rayozzie/redbee/Photos/20160505_203314.jpg

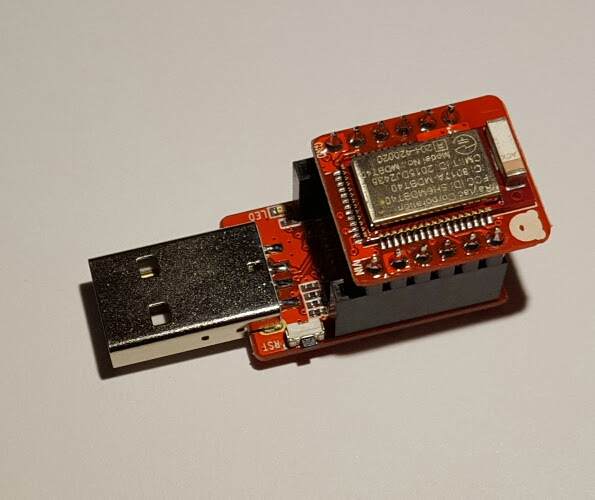
Photos/20160505_203314.jpg
