rayozzie/redbee/Photos/20160505_203927.jpg

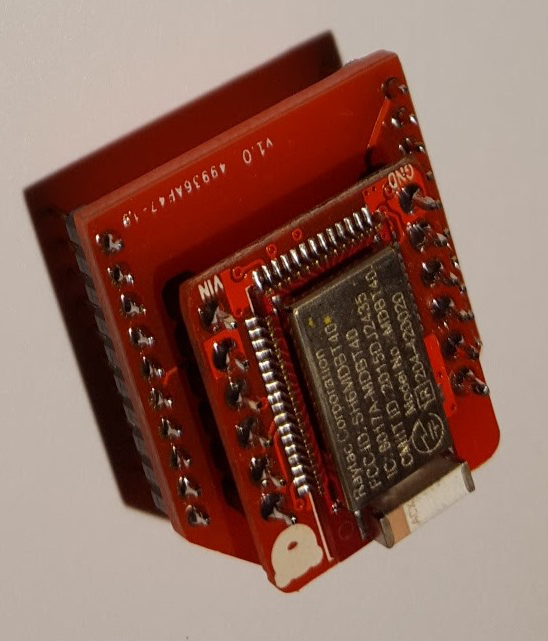
Photos/20160505_203927.jpg
