rayozzie/redbee/Photos/20160505_203952.jpg

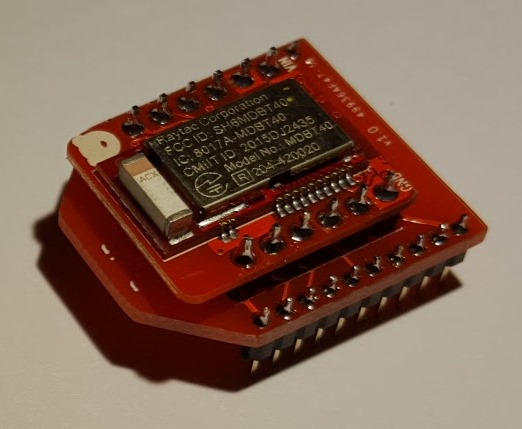
Photos/20160505_203952.jpg
