rayozzie/redbee/Photos/20160505_204019.jpg

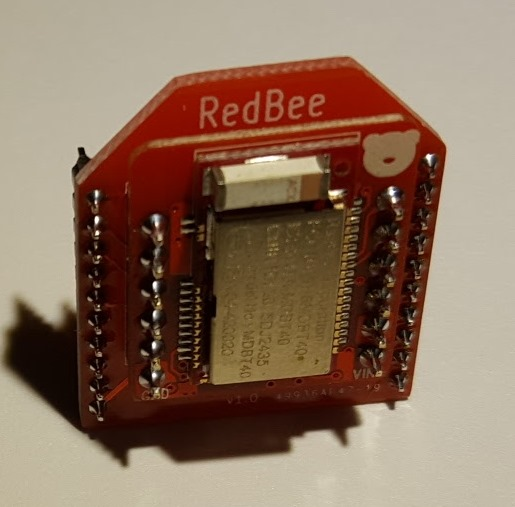
Photos/20160505_204019.jpg
