rayozzie/redbee/Photos/20160505_204045.jpg

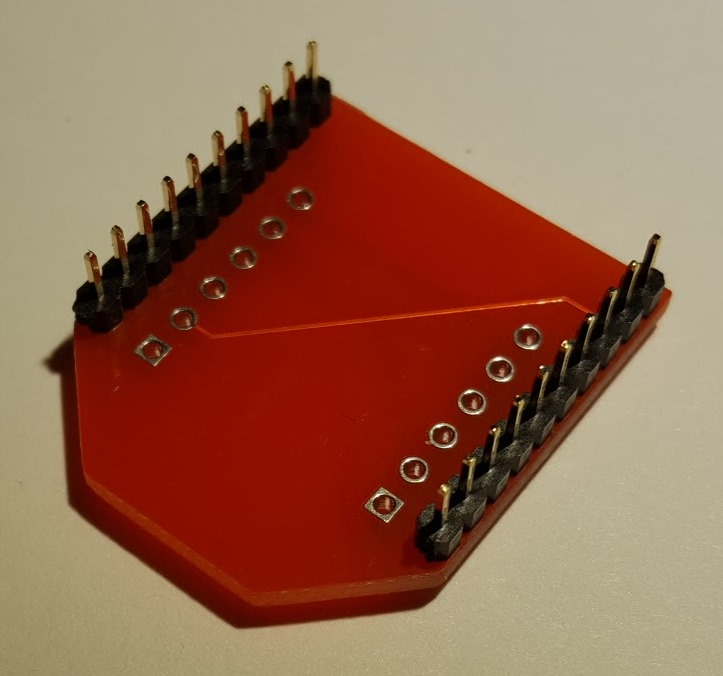
Photos/20160505_204045.jpg
