rayozzie/redbee/Photos/20160505_204118.jpg

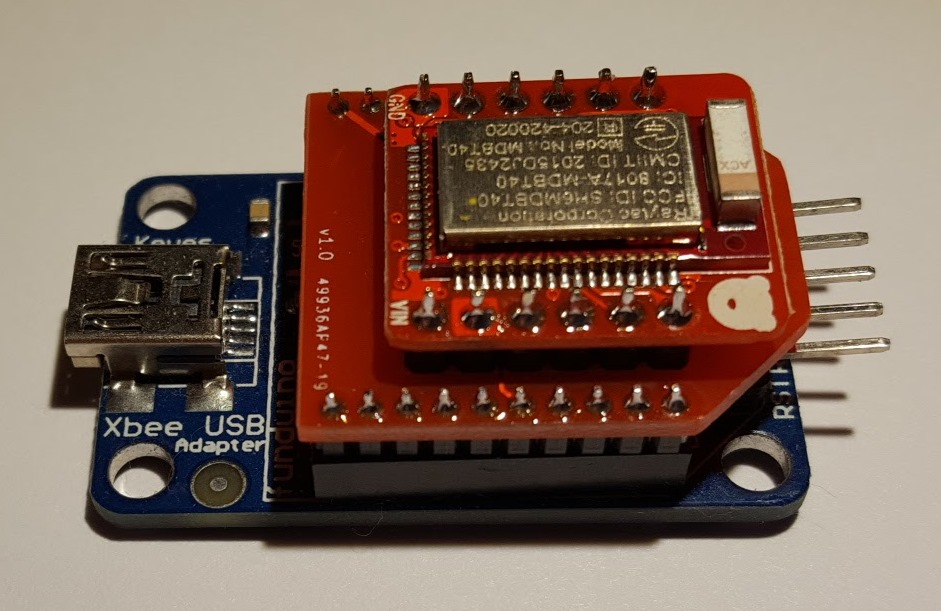
Photos/20160505_204118.jpg
