rayozzie/redbee/Photos/20160505_204125.jpg

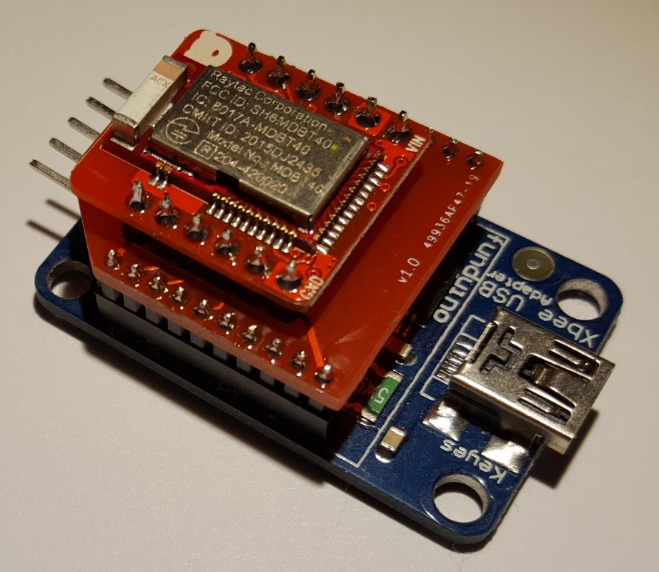
Photos/20160505_204125.jpg
