rayozzie/redbee/Photos/20160505_204313.jpg

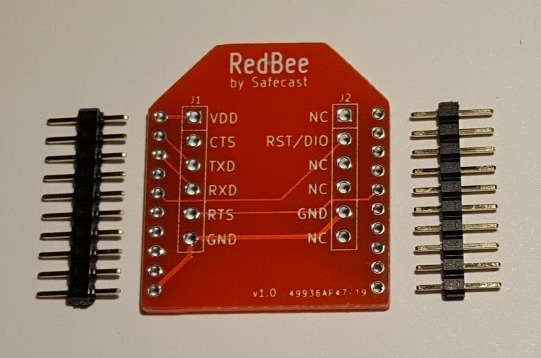
Photos/20160505_204313.jpg
