rayozzie/redbee/Photos/20160505_204332.jpg

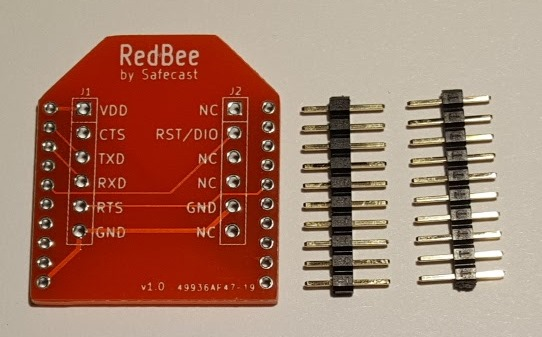
Photos/20160505_204332.jpg
