rayozzie/redbee/Photos/20160505_204348.jpg

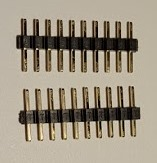
Photos/20160505_204348.jpg
