rayozzie/redbee/Photos/20160505_204400.jpg

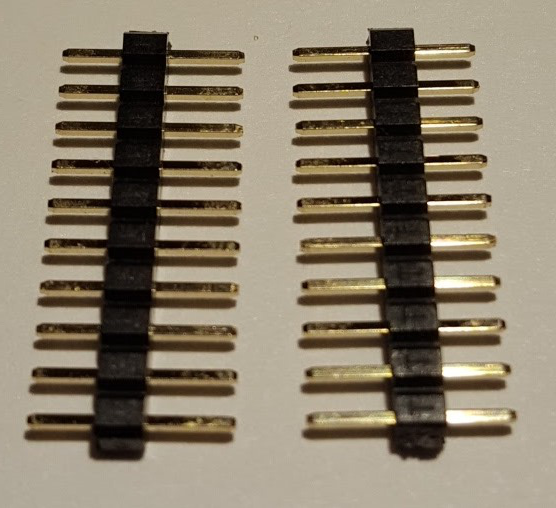
Photos/20160505_204400.jpg
