rayozzie/redbee/Rendered_Pics/Bare_PCB/RedBee_Back_Bare_small.png

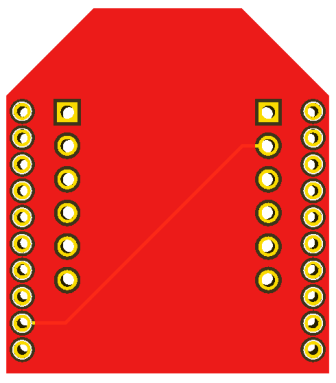
Rendered_Pics/Bare_PCB/RedBee_Back_Bare_small.png
