rayozzie/redbee/Rendered_Pics/Bare_PCB/RedBee_Front_ISO2_Bare_small.png

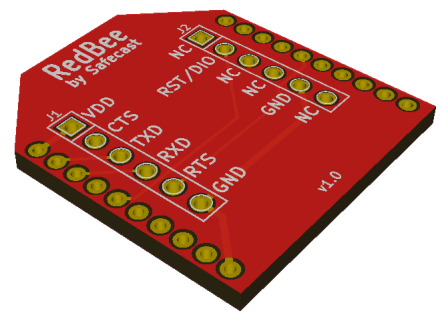
Rendered_Pics/Bare_PCB/RedBee_Front_ISO2_Bare_small.png
