rayozzie/redbee/Rendered_Pics/Bare_PCB/RedBee_Layout_edited.png

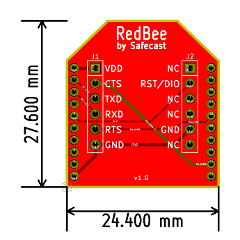
Rendered_Pics/Bare_PCB/RedBee_Layout_edited.png
