rayozzie/redbee/Rendered_Pics/RedBee_Front.png

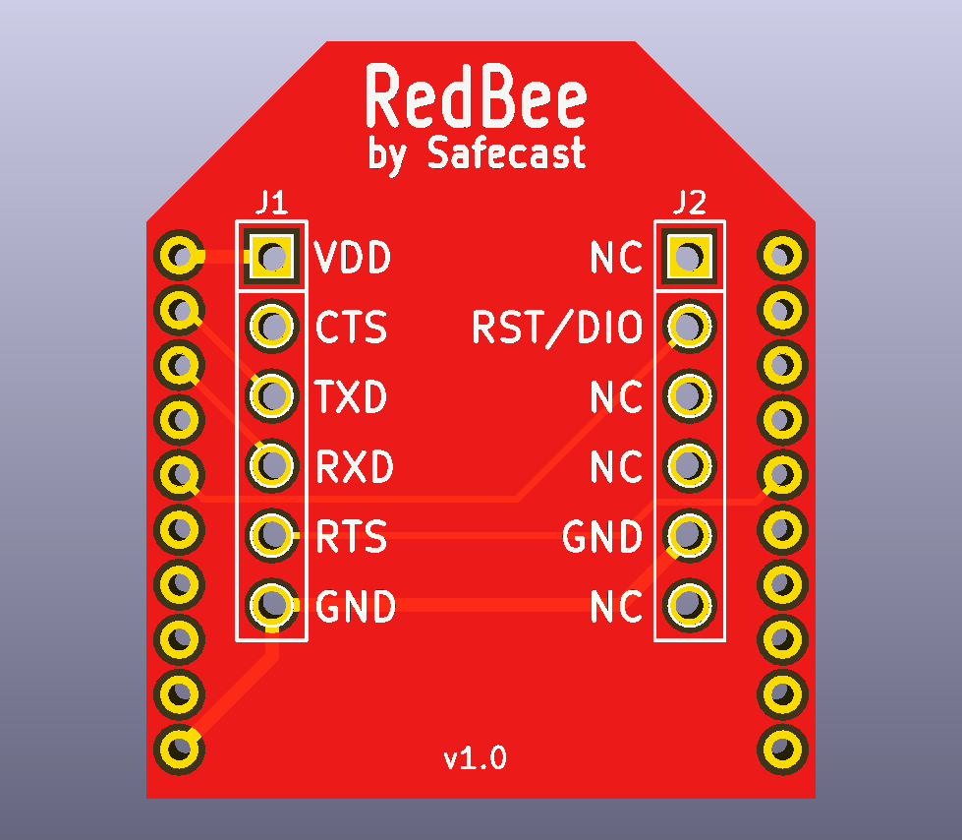
Rendered_Pics/RedBee_Front.png
